jef238/jefBoard/Tutorial/basic_blinker/firmware/main.c

/* Name: main.c
 * Author: g.culotta *
 */

#include <avr/io.h>
#include <util/delay.h>

int main(void)
{
    //Setup
    DDRB |= (1 << PB0) | (1 << PB1) | (1 << PB2); //Set  as OUTPUT
    
    while(1){
        int i;
        for (i=0;i<3;i++){
        PORTB |= (1 << i);
        _delay_ms(50);
        PORTB &= ~(1 <<i);
        _delay_ms(50);
        }
    }
    return 0;   /* never reached */
}
